rojinaks/diy-particle-detector-V2/codes/auslese/oszi_20250616_210128.png

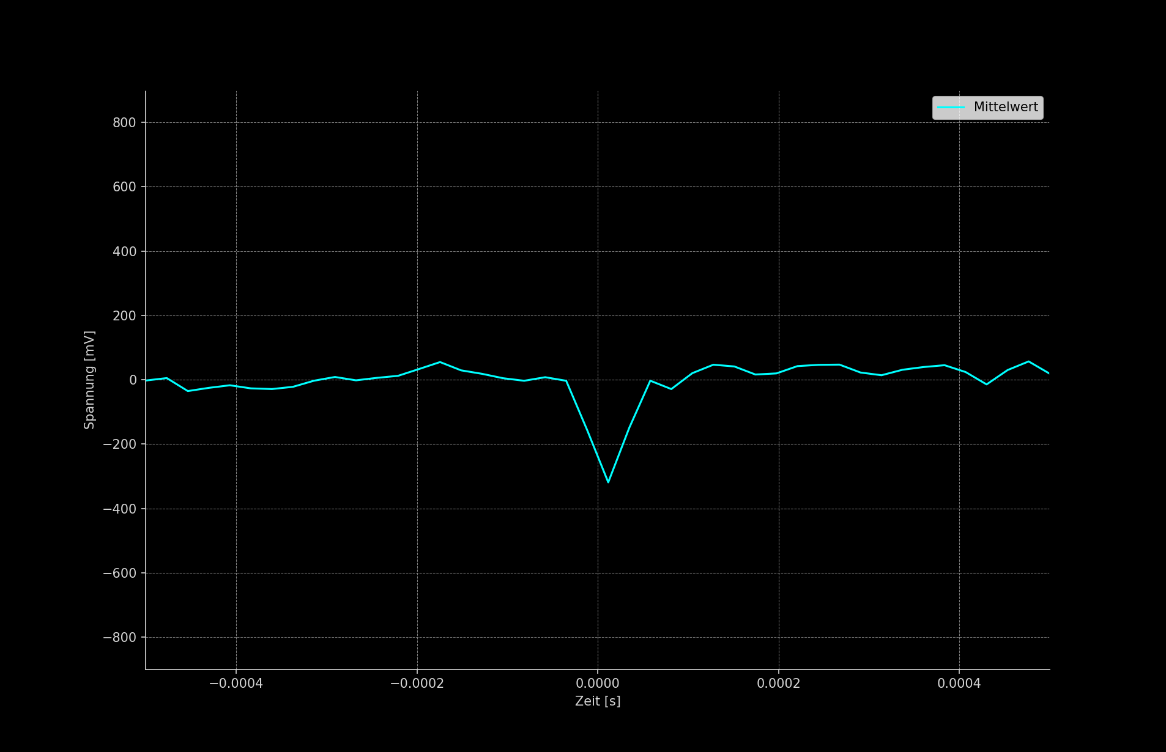
codes/auslese/oszi_20250616_210128.png
