rojinaks/diy-particle-detector-V2/codes/auslese/oszi_20250812_132204.png

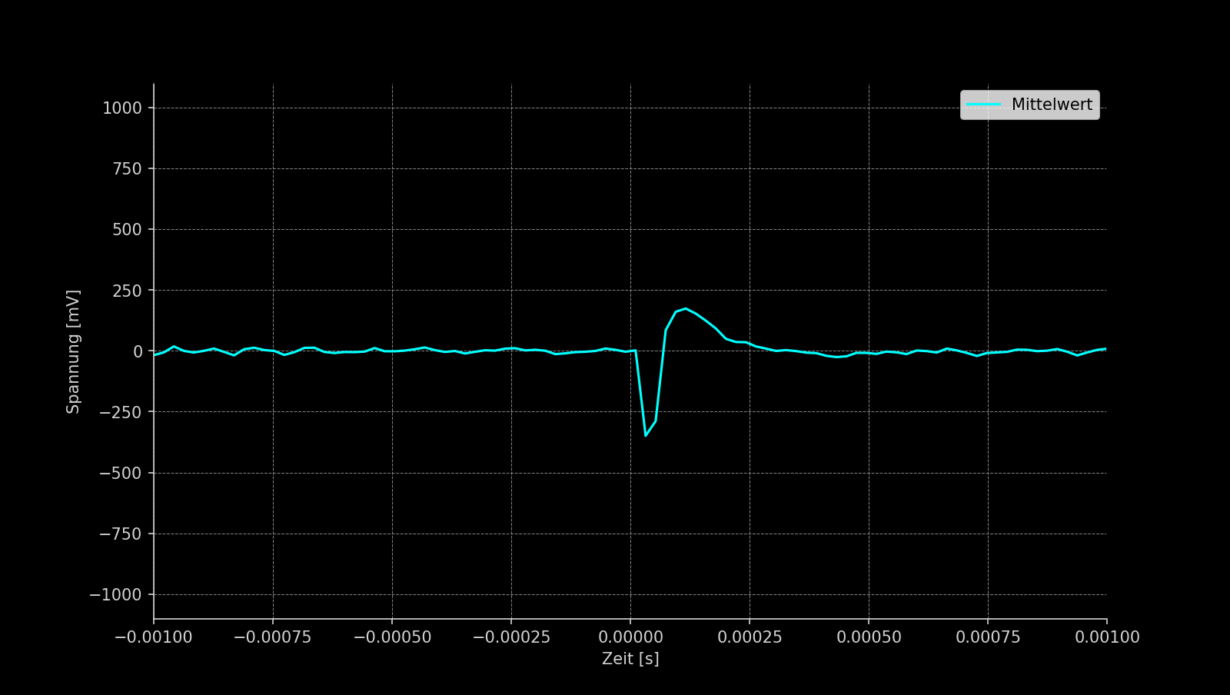
codes/auslese/oszi_20250812_132204.png
