rojinaks/diy-particle-detector-V2/codes/diode/CvsU.png

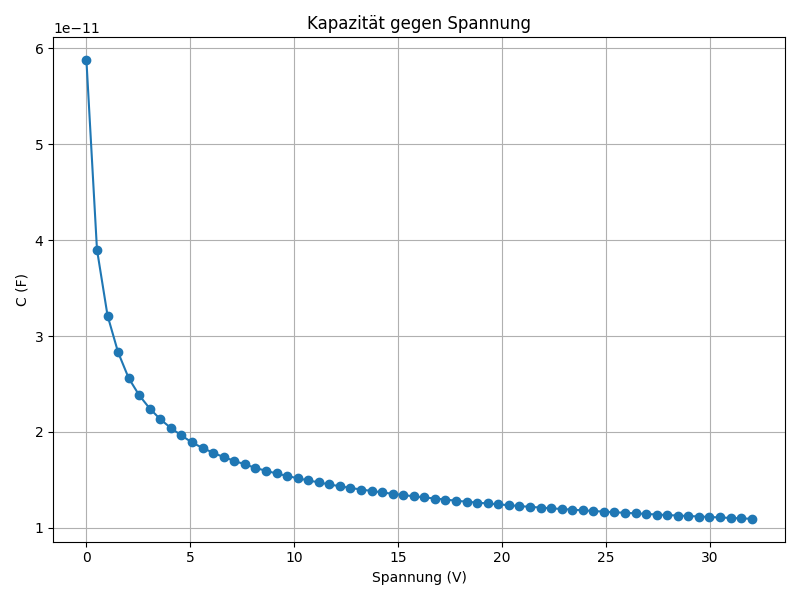
codes/diode/CvsU.png
