rojinaks/diy-particle-detector-V2/codes/auslese/test/oszi_average_20250523_121021.csv

Zeit [s] | gemittelte Spannung [mV]
0.0 | -9.8108
2.269790288223468e-05 | -7.721274
4.539580576446936e-05 | -7.6273403
6.809370864670405e-05 | -9.30026
9.079161152893873e-05 | -9.838408
0.0001134895144111734 | -8.323601
0.0001361874172934081 | -6.6381936
0.00015888532017564277 | -5.8599224
0.00018158322305787745 | -4.640615
0.00020428112594011213 | -1.9459425
0.0002269790288223468 | 0.72179365
0.0002496769317045815 | 1.2628546
0.0002723748345868162 | -0.015588631
0.00029507273746905084 | -0.8106455
0.00031777064035128555 | 0.15881073
0.0003404685432335202 | 1.8181471
0.0003631664461157549 | 2.5344136
0.0003858643489979896 | 2.1893504
0.00040856225188022426 | 1.8172611
0.00043126015476245897 | 1.7857136
0.0004539580576446936 | 1.3550953
0.0004766559605269283 | 0.144503
0.000499353863409163 | -0.9276018
0.0005220517662913977 | -0.88064194
0.0005447496691736324 | -0.2924188
0.0005674475720558671 | -0.68575007
0.0005901454749381017 | -2.4035616
0.0006128433778203364 | -4.0998206
0.0006355412807025711 | -4.522798
0.0006582391835848058 | -3.8349712
0.0006809370864670404 | -2.824886
0.0007036349893492751 | -1.8703133
0.0007263328922315098 | -1.3121053
0.0007490307951137445 | -1.7629814
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
