rojinaks/diy-particle-detector-V2/codes/auslese/test/oszi_average_20250526_124620.csv

Zeit [s] | gemittelte Spannung [mV]
-0.001 | -1.0979884
-0.0009770114942528735 | -15.359304
-0.0009540229885057471 | 48.088676
-0.0009310344827586207 | 31.246693
-0.0009080459770114943 | -0.5444397
-0.0008850574712643679 | 22.311174
-0.0008620689655172414 | 23.856081
-0.000839080459770115 | -42.637142
-0.0008160919540229886 | -36.165447
-0.000793103448275862 | -18.242754
-0.0007701149425287356 | -20.526386
-0.0007471264367816092 | -7.892619
-0.0007241379310344827 | 0.39194337
-0.0007011494252873564 | 11.315213
-0.0006781609195402299 | -49.629967
-0.0006551724137931035 | 11.896425
-0.0006321839080459771 | 48.633965
-0.0006091954022988506 | 57.236805
-0.0005862068965517242 | 98.98433
-0.0005632183908045978 | -37.254936
-0.0005402298850574712 | -55.037262
-0.0005172413793103448 | -48.11671
-0.0004942528735632184 | -46.46833
-0.00047126436781609203 | -34.28192
-0.0004482758620689655 | 0.58478546
-0.0004252873563218391 | 15.215775
-0.0004022988505747127 | -14.921305
-0.0003793103448275862 | 84.280174
-0.0003563218390804598 | 2.2774088
-0.0003333333333333334 | -37.67383
-0.00031034482758620697 | 9.130128
-0.00028735632183908046 | 26.938885
-0.00026436781609195405 | 30.122416
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
