rojinaks/diy-particle-detector-V2/codes/auslese/test/oszi_20250522_195807.png

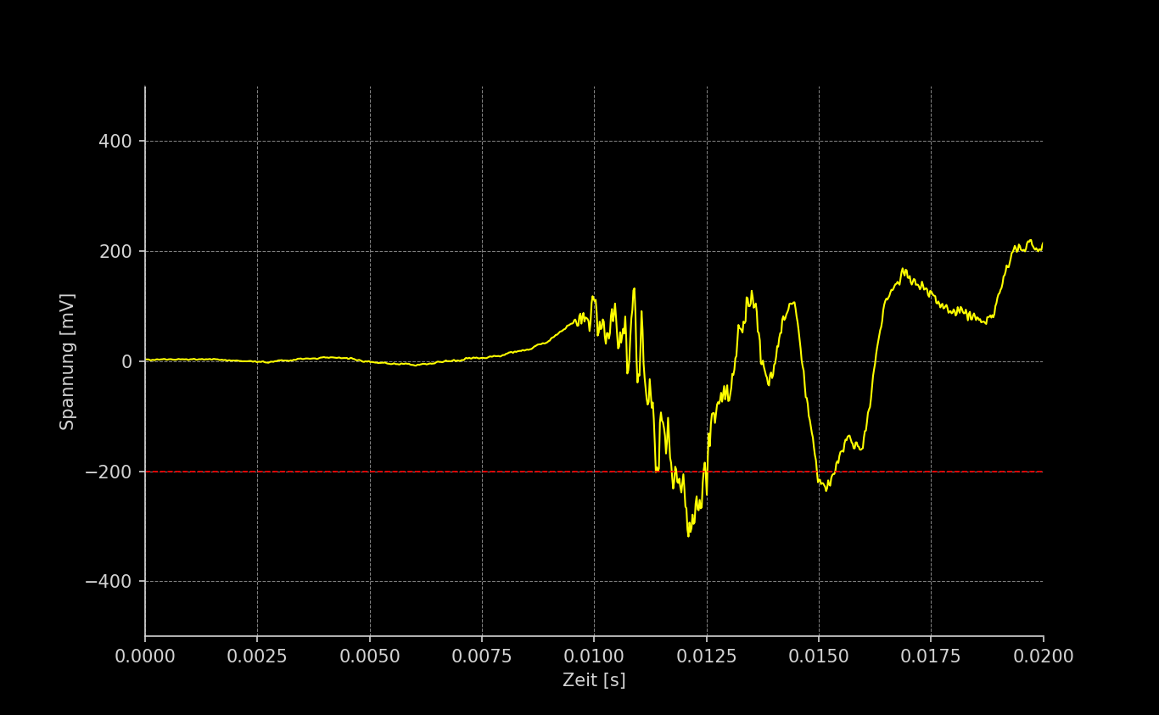
codes/auslese/test/oszi_20250522_195807.png
