rojinaks/diy-particle-detector-V2/codes/auslese/test/oszi_20250522_201757.png

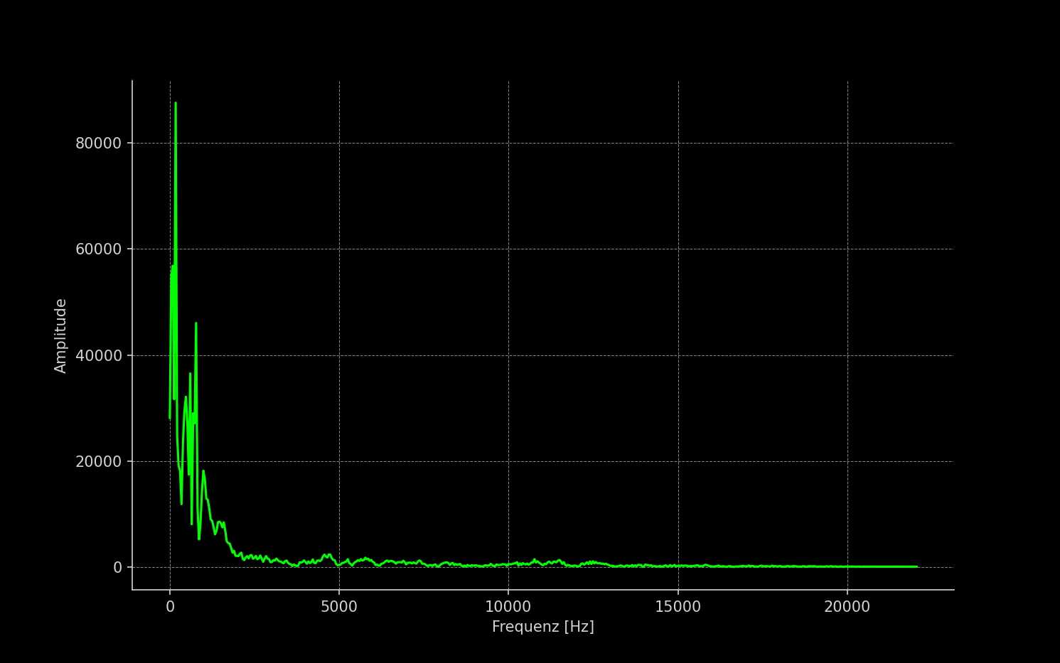
codes/auslese/test/oszi_20250522_201757.png
