rojinaks/diy-particle-detector-V2/codes/auslese/test/oszi_20250522_203317.png

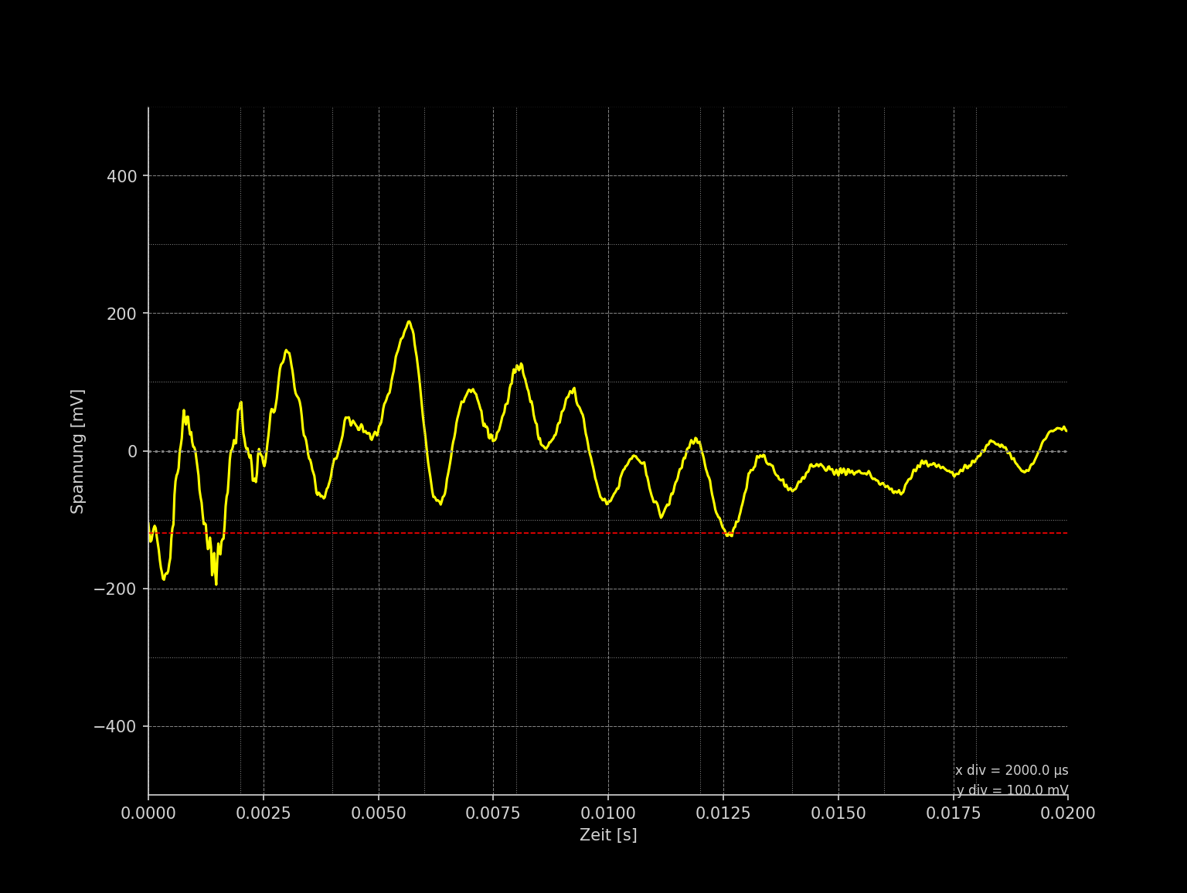
codes/auslese/test/oszi_20250522_203317.png
