rojinaks/diy-particle-detector-V2/codes/auslese/test/oszi_20250522_212541.png

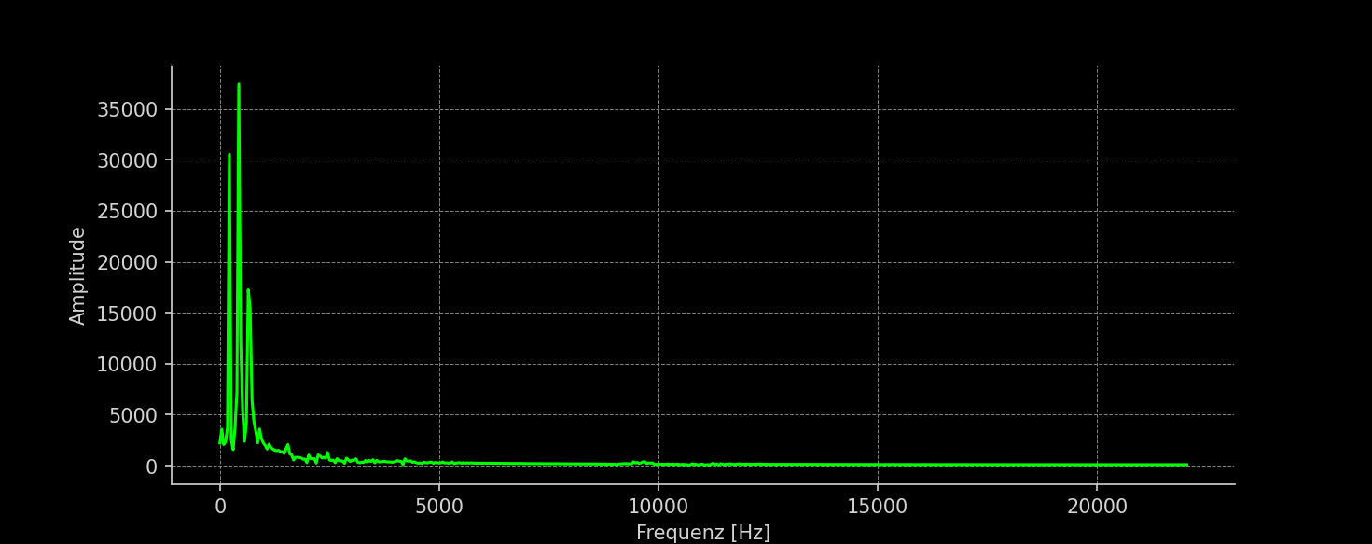
codes/auslese/test/oszi_20250522_212541.png
