rojinaks/diy-particle-detector-V2/codes/auslese/test/oszi_20250523_115505.png

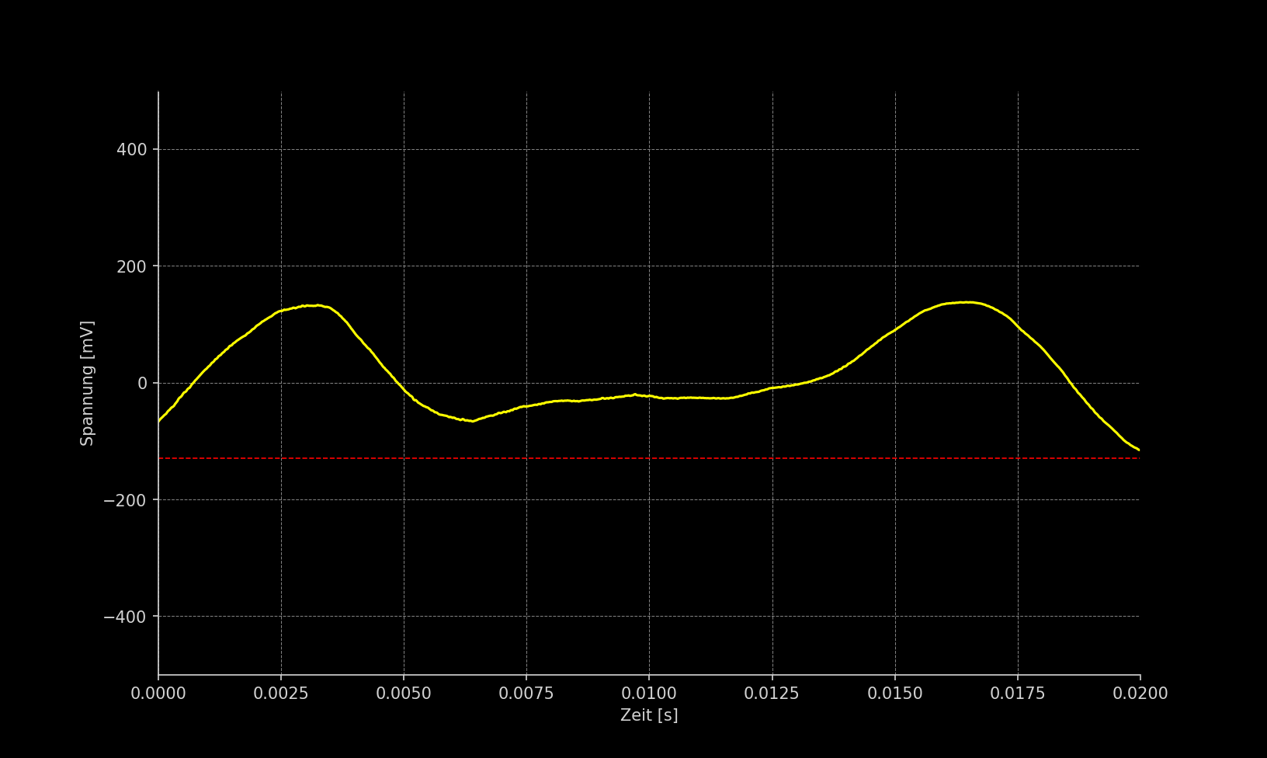
codes/auslese/test/oszi_20250523_115505.png
