rojinaks/diy-particle-detector-V2/codes/Signal tests/messungen2_4/Tek001_004.png

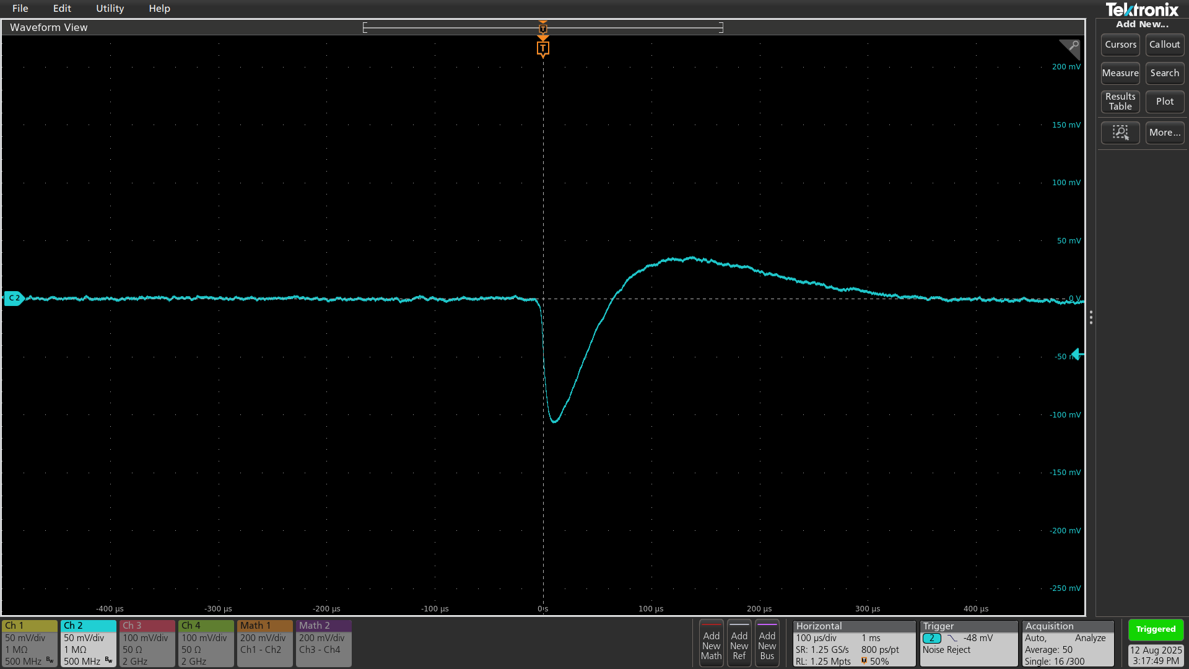
codes/Signal tests/messungen2_4/Tek001_004.png
