rojinaks/diy-particle-detector-V2/hardware/spice/detector_test2.asc

C1: cap; 10p
C2: cap; 10p
C3: cap; 100n
C4: cap; 100n
C5: cap; 10p
C6: cap; 100n
C7: cap; 100n
C8: cap; 47µ
C10: Cap; 10p
D1: diode
D2: diode
D3: diode
D4: diode
R1: res; 4.7k
R2: res; 15k
R3: res; 10Mega
R4: res; 1k
R5: res; 100K
R6: res; 10k
R7: res; 10k
R8: res; 0
R9: res; 100k
U1: TLE2072; OPAx828
U2: TLE2072; OPAx828
V1: voltage; 9
V2: Voltage; PULSE(0 -40.3u 0.5m 300p 10p 1 1 1)
Named nets: 0, VCC, input, output
.include /Users/rojinaksu/Library/Application Support/LTspice/lib/sub/OPAx828.lib
.tran 1m
.lib OPAx828.lib
