rojinaks/diy-particle-detector-V2/hardware/spice/detector_test1.asc

C1: cap; 10p
C2: cap; 10p
C3: cap; 100n
C4: cap; 100n
C5: cap; 10p
C6: cap; 100n
C7: cap; 100n
C8: cap; 47µ
C10: Cap; 10p
D1: diode
D2: diode
D3: diode
D4: diode
R1: res; 4.7k
R2: res; 15k
R3: res; 10Mega
R4: res; 1k
R5: res; 100K
R6: res; 10k
R7: res; 10k
R8: res; 0
R9: res; 25k
U1: AD8091
U2: AD8091
V1: voltage; 9
V2: Voltage; PULSE(0 -40.3u 0.5m 300p 10p 1 1 1)
Named nets: 0, VCC, input, output
.include /Users/rojinaksu/Library/Application Support/LTspice/lib/sub/TLE2072.lib
.tran 0 1m 0 50n
;.noise V(output) VAC dec 100 1 1Meg
;BNOISE input 0 V=white(1)
BINPUT input 0 V=PULSE(0 -0.3 0.5m 300p 10p 1 1) + white(0.2)
