rojinaks/diy-particle-detector-V2/hardware/spice/detector2.asc

C1: cap; 5p
C2: cap; 100n
C4: cap; 100n
C5: cap; 10p
C7: cap; 10n
C8: cap; 47µ
C10: Cap; 10p
D1: diode
D2: diode
D3: diode
D4: diode
R1: res; 4.7k
R2: res; 15k
R3: res; 100Mega
R4: res; 1k
R5: res; 100k
R6: res; 10k
R7: res; 10k
R8: res; 2.2k
U1: opamp2; lmx58_lm2904
U2: opamp2; lmx58_lm2904
V1: voltage; 9
V2: Voltage; PULSE(0 -40.3u 0.5 300p 10p 1 1 1)
Named nets: 0, VCC, input, output
.include /Users/rojinaksu/Library/Application Support/LTspice/lib/sub/lmx58_lm2904.lib
.tran 1
.lib lmx58_lm2904.lib
