rojinaks/diy-particle-detector-V2/hardware/spice/Draft1.asc

C1: cap; 10p
C2: cap; 10p
C3: cap
C4: cap; 100n
C5: cap; 10p
C6: cap; 100n
C7: cap; 100n
C8: cap; 47mikro
R1: res; 4.7k
R2: res; 15k
R3: res; 10Mega
R4: res; 1k
R5: res; 100K
R6: res; 10k
R7: res; 10k
R8: res; 0
R9: res; 2.2k
U1: UniversalOpAmp2
U2: UniversalOpAmp2
V1: voltage; 9
Named nets: 0, VCC
.lib "/Users/rojinaksu/Library/Application Support/LTspice/lib/sub/TLE2072.lib"
